tomcircuit/HP_classic/media/HP_classic_top.jpg

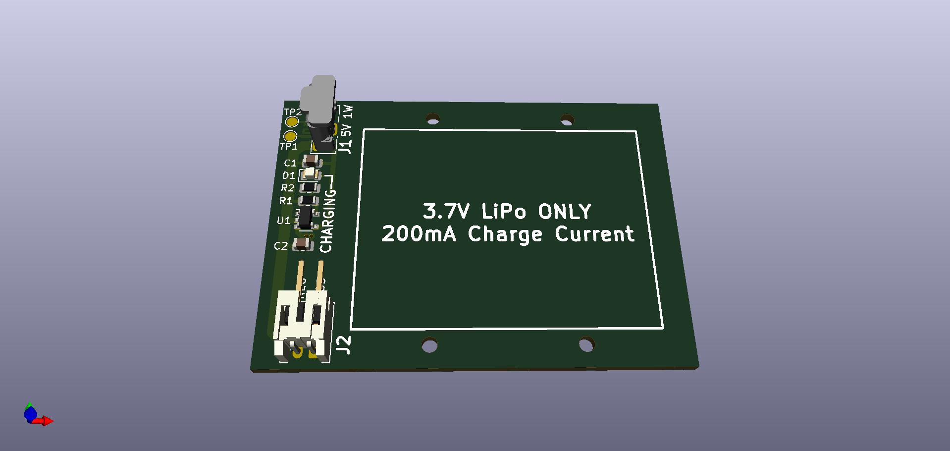
media/HP_classic_top.jpg
