tomcircuit/HP_classic/media/topside.jpg

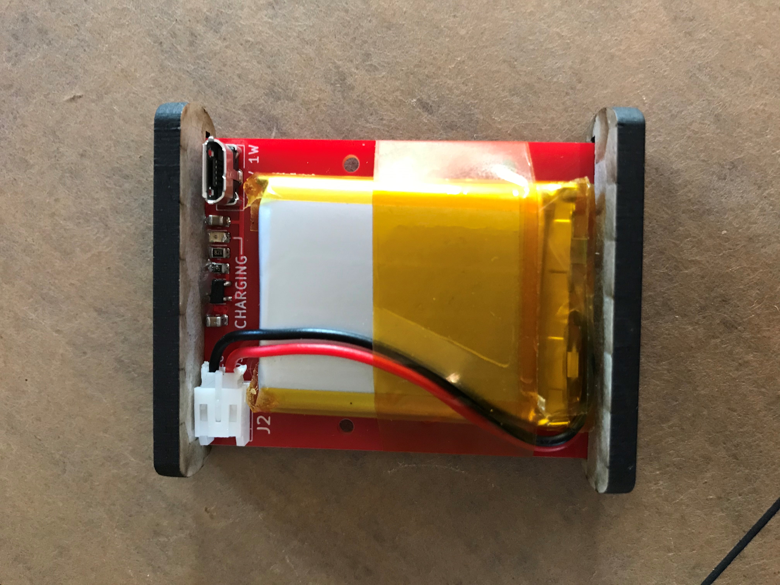
media/topside.jpg
