tomcircuit/HP_classic/media/underside.jpg

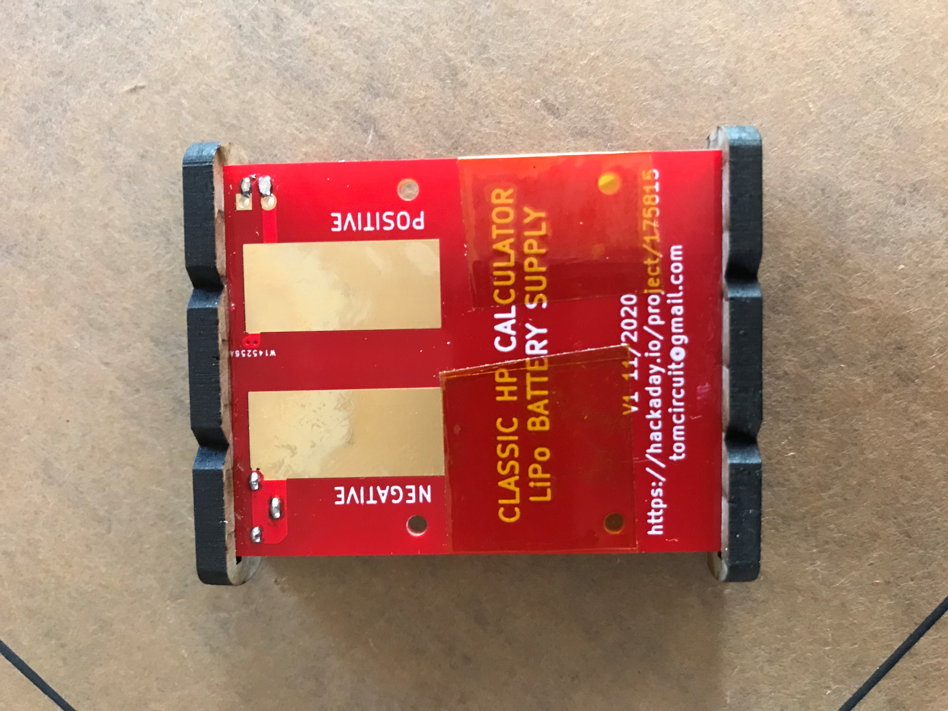
media/underside.jpg
