tomcircuit/HP_classic/simulation/waveforms.png

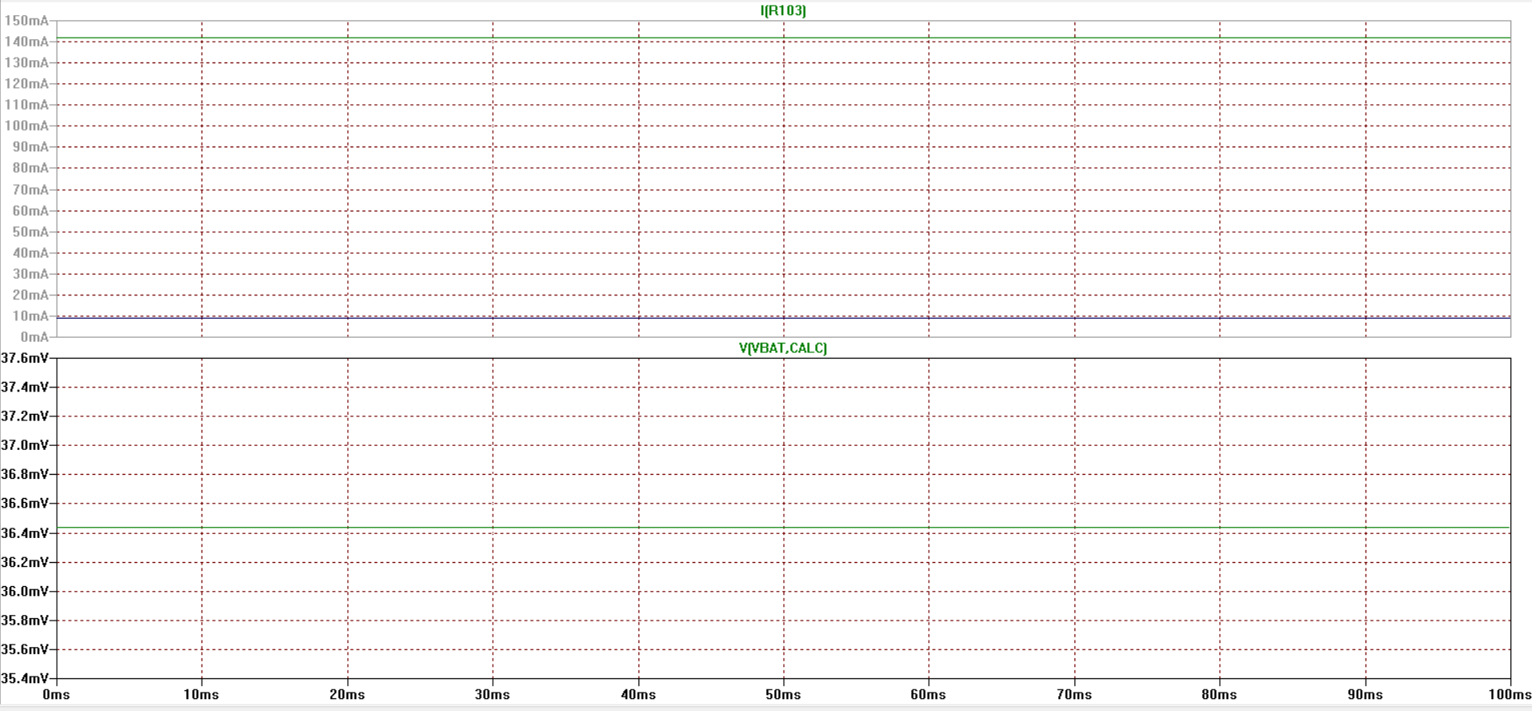
simulation/waveforms.png
