tomcircuit/HP_classic/simulation/HP_charger_rev_pol_MAX40203.asc

D1: zener; DI_MMSZ5231B
D2: zener; DI_MMSZ5231B
Q1: npn; 2N3904
Q2: pnp; 2N3906
Q3: pnp; 2N3906
R2: res; 470
R3: res; 470
R4: res; 13
R100: res; {RAC}
R101: res; {RAC}
R102: res; {RDC}
R103: res; 0.01
R104: res; 27
R105: res; 100K
U1: MAX40203
V1: voltage; 3.7; Rser=0.5
V3: voltage; 24
Named nets: CALC, 0, CHARGE, VREG, GROUND, VBAT
.tran 100m
.lib mmsz5231.sub
.PARAM CHARGER=0
.PARAM RAC=0.01+(100MEG-100MEG*{CHARGER})
.PARAM RDC=0.01+(100MEG*{CHARGER})
Configuration
HP AC Adapter Model
Set "CHARGER=1" for AC Adapter usecase
Set "CHARGER=0" for LiPo usecase
Calc. Load
LiPo 3.7V
Reverse Current Protection
25-NOV-2020
T. LeMense
HP Classic Battery Pack - Reverse Current Protection
Observe: V(VBAT,CALC) and I(R103) for both cases
Goal 1: minimal V(VBAT,CALC) when CHARGER=0
Goal 2: minimal I(R103) when CHARGER=1
Note: tweaked R3 to obtain ~50mA of charge current
.step param CHARGER list 0 1
